Xtalism/pen-plotter-marlin/SLDPRT/CNC_FINAL.SLDASM

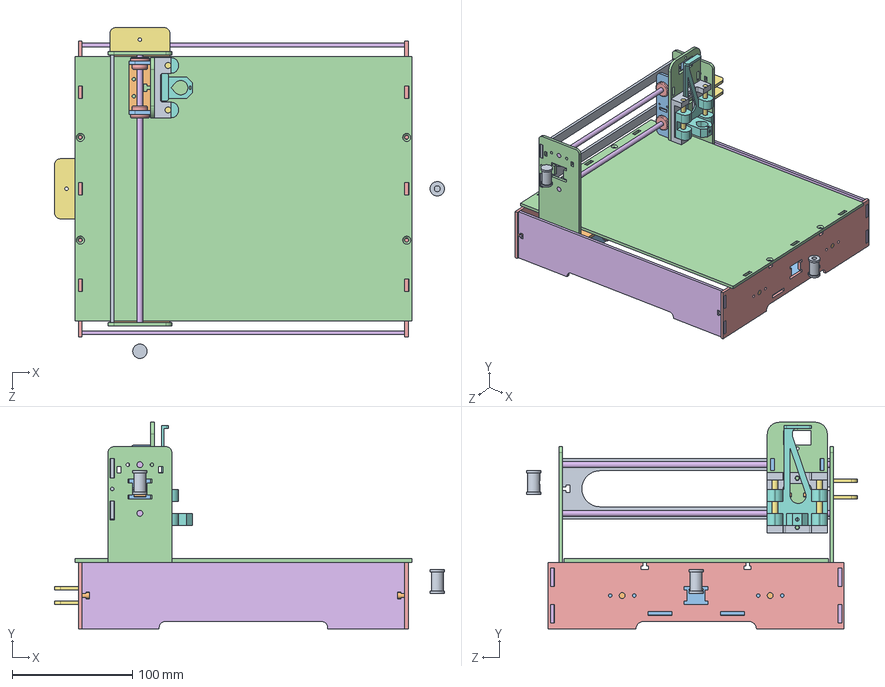
[picture p44: CAD file, 2025-09-09]
SLDPRT/CNC_FINAL.SLDASM
324.1 x 171.7 x 275.0 mm
SoporteY_CNC x 2
SoporteBuje_CNC x 2
BaseY
FronteY_CNC
SoportePequeno_CNC x 2
BASERODAMIENTO_CNC x 4
EjeCY_CNC x 2
Bujepr_CNC x 8
SoporteZ_CNC
SoporteTZ_CNC x 2
SoporteZP_CNC
BaseLapiz_CNC
EjeMovil_CNC
CilindroY_CNC x 2
Laterales_CNC x 2
Frontales_CNC x 2
Base_CNC
Soporte_CNC
CilindroX_CNC x 2
Buje_Motor_CNC x 2
