Xtalism/pen-plotter-marlin/SLDPRT/SoporteTZ_CNC.SLDPRT

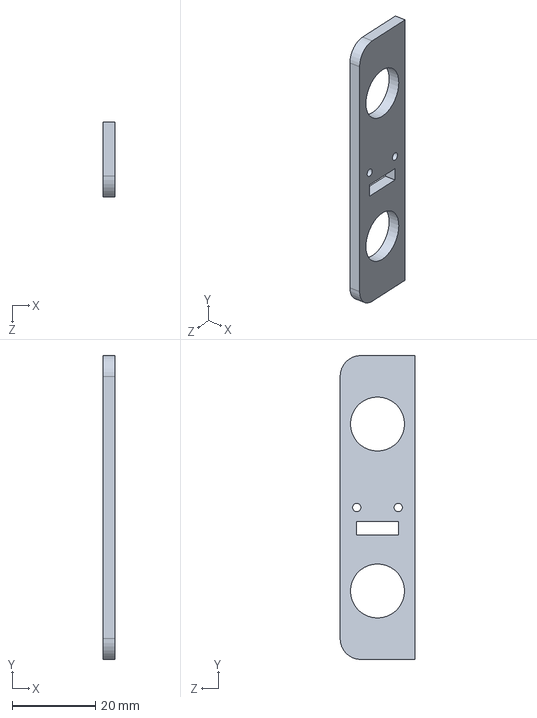
[picture p58: CAD file, 2025-09-09]
SLDPRT/SoporteTZ_CNC.SLDPRT
3.00 x 73.2 x 18.0 mm
