Xtalism/pen-plotter-marlin/SLDPRT/SoporteY_CNC.SLDPRT

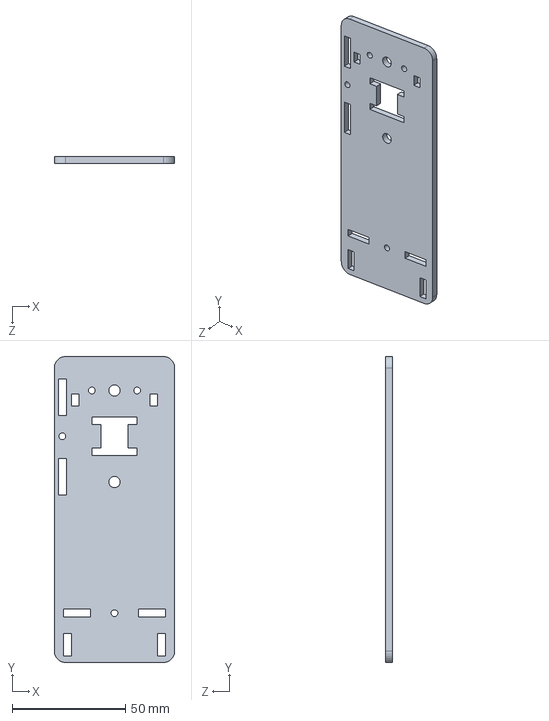
[picture p59: CAD file, 2025-09-09]
SLDPRT/SoporteY_CNC.SLDPRT
53.1 x 135.0 x 3.00 mm
