Xtalism/pen-plotter-marlin/SLDPRT/BaseLapiz_CNC.SLDPRT

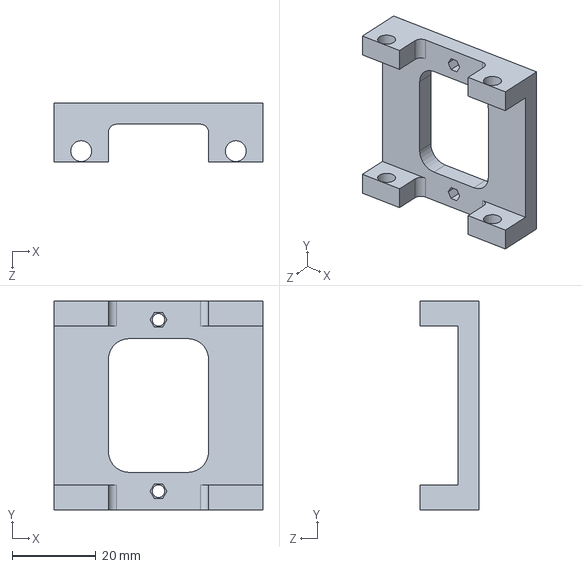
[picture p60: CAD file, 2025-09-09]
SLDPRT/BaseLapiz_CNC.SLDPRT
50.0 x 50.0 x 14.0 mm
