Xtalism/pen-plotter-marlin/SLDPRT/BaseY.SLDPRT

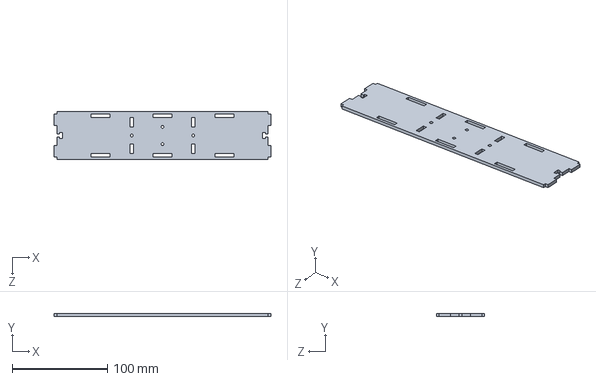
[picture p61: CAD file, 2025-09-09]
SLDPRT/BaseY.SLDPRT
228.0 x 3.00 x 50.0 mm
