Xtalism/pen-plotter-marlin/SLDPRT/SoporteZP_CNC.SLDPRT

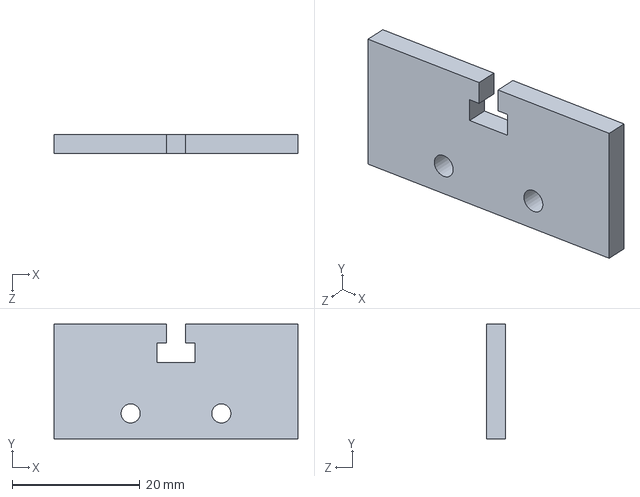
[picture p62: CAD file, 2025-09-09]
SLDPRT/SoporteZP_CNC.SLDPRT
38.2 x 18.0 x 3.00 mm
