Xtalism/pen-plotter-marlin/SLDPRT/CilindroX_CNC.SLDPRT

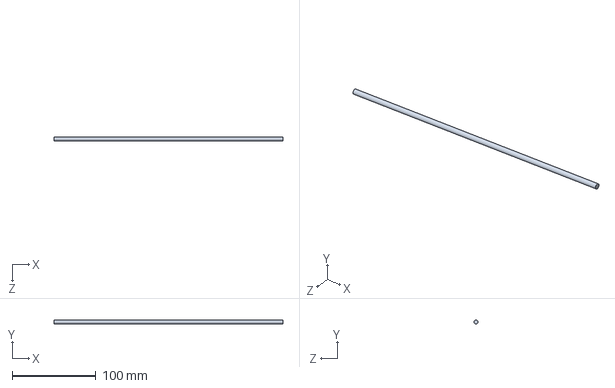
[picture p63: CAD file, 2025-09-09]
SLDPRT/CilindroX_CNC.SLDPRT
274.0 x 5.00 x 5.00 mm
