Xtalism/pen-plotter-marlin/SLDPRT/BASERODAMIENTO_CNC.SLDPRT

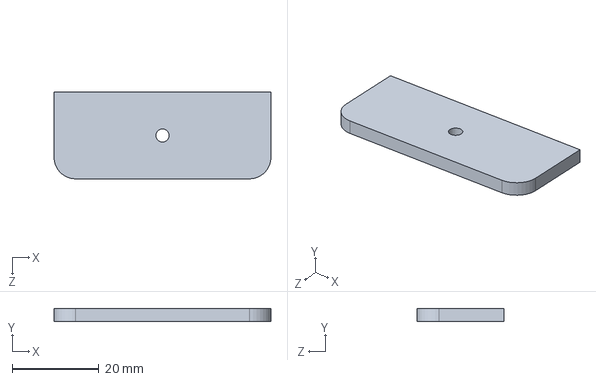
[picture p64: CAD file, 2025-09-09]
SLDPRT/BASERODAMIENTO_CNC.SLDPRT
50.0 x 3.00 x 20.0 mm
