Xtalism/pen-plotter-marlin/SLDPRT/SoporteMotor_CNC.SLDPRT

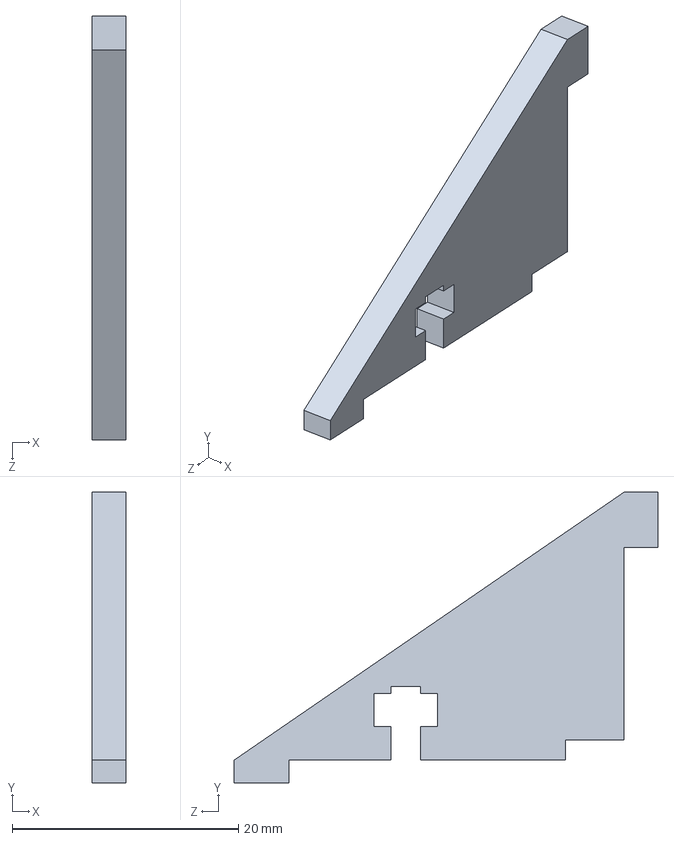
[picture p65: CAD file, 2025-09-09]
SLDPRT/SoporteMotor_CNC.SLDPRT
3.00 x 25.7 x 37.5 mm
