Xtalism/pen-plotter-marlin/SLDPRT/EjeMovil_CNC.SLDPRT

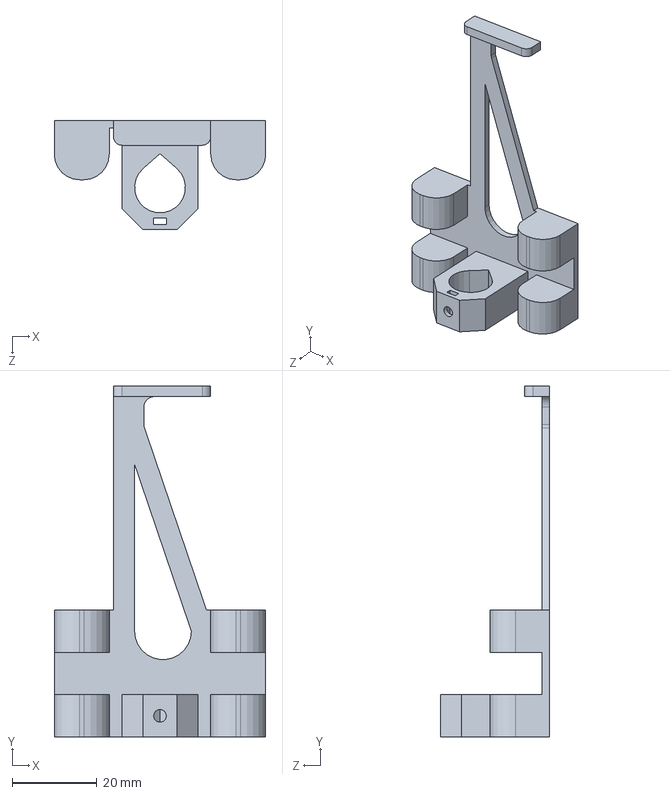
[picture p66: CAD file, 2025-09-09]
SLDPRT/EjeMovil_CNC.SLDPRT
50.0 x 83.0 x 25.9 mm
