Xtalism/pen-plotter-marlin/SLDPRT/EjeCY_CNC.SLDPRT

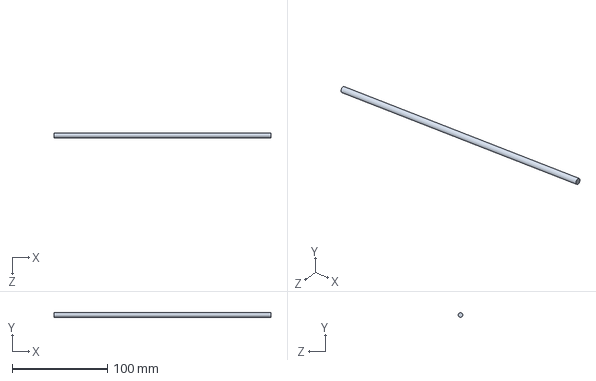
[picture p67: CAD file, 2025-09-09]
SLDPRT/EjeCY_CNC.SLDPRT
228.0 x 5.00 x 5.00 mm
