Xtalism/pen-plotter-marlin/SLDPRT/Blueprints/EJE Z.pdf

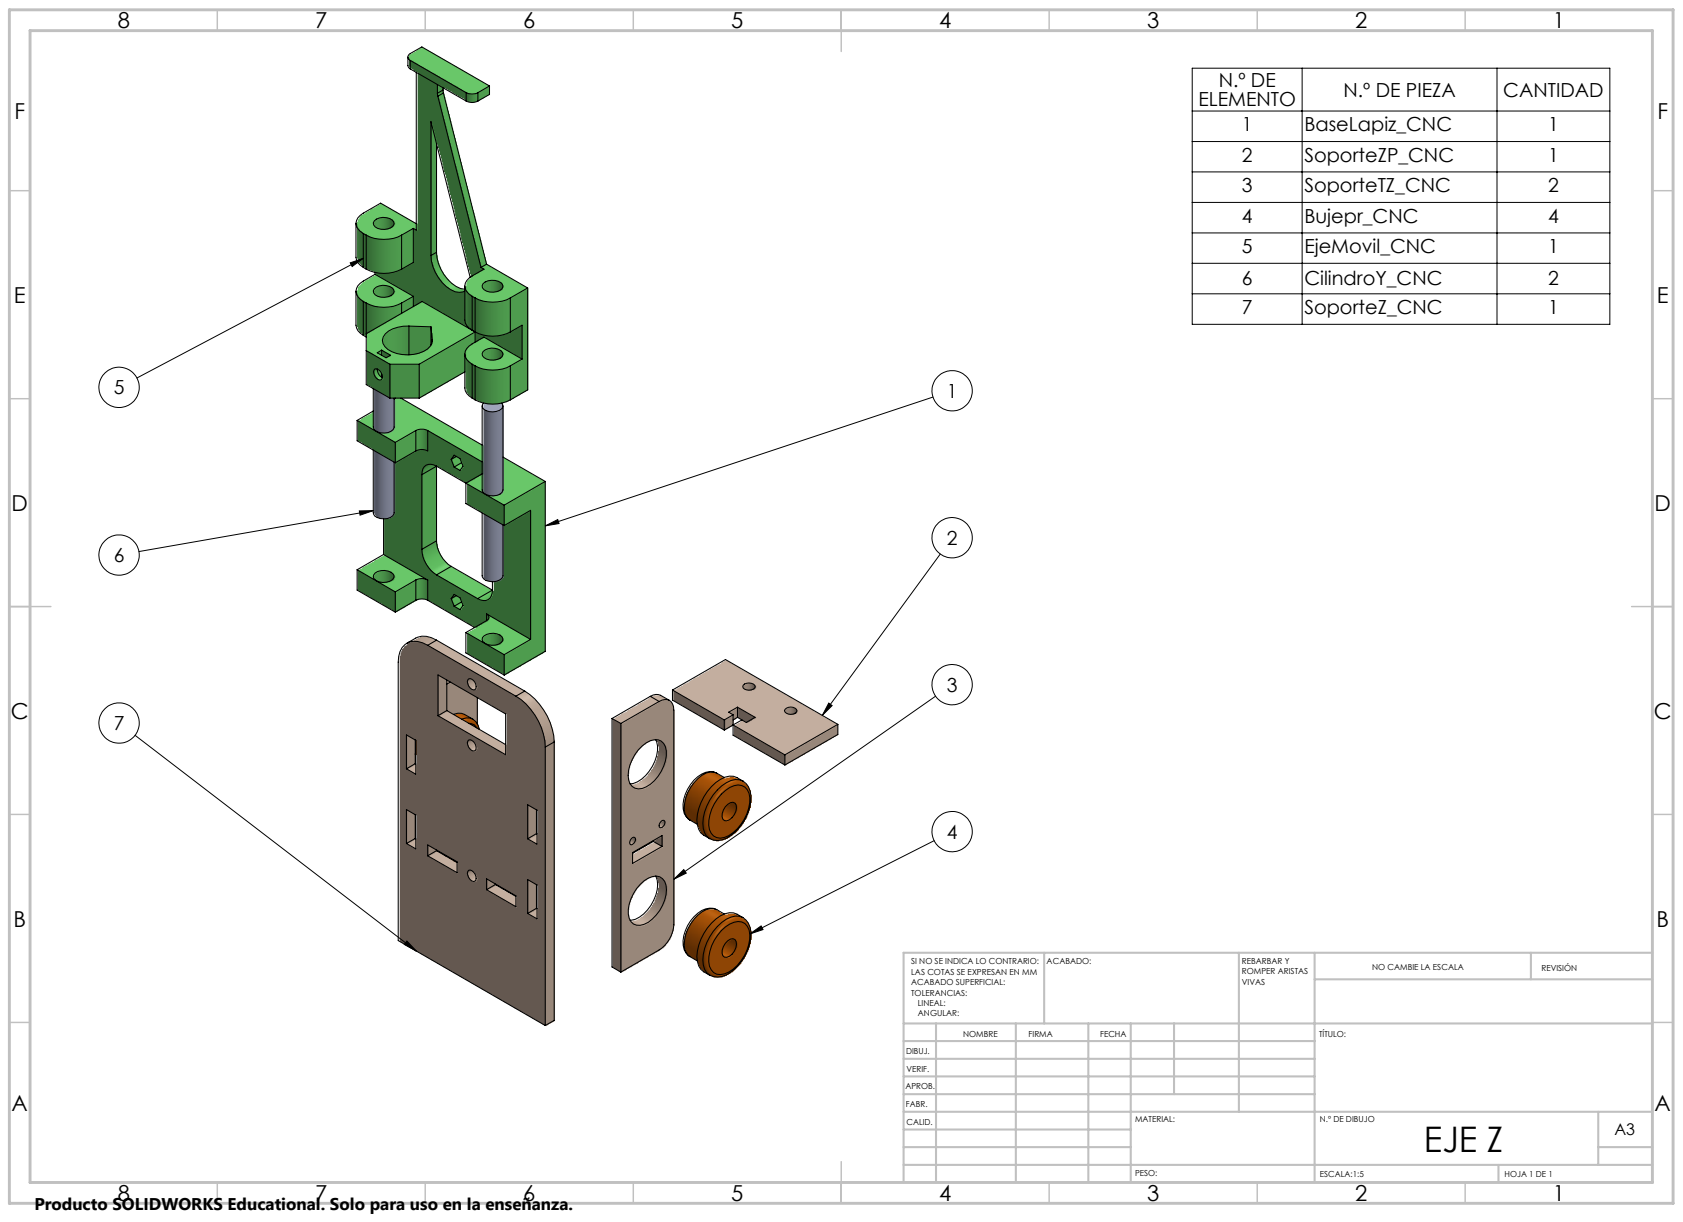
[picture p75: page 1]
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

N.º DE ELEMENTO | N.º DE PIEZA | CANTIDAD
1 | BaseLapiz_CNC | 1
2 | SoporteZP_CNC | 1
3 | SoporteTZ_CNC | 2
4 | Bujepr_CNC | 4
5 | EjeMovil_CNC | 1
6 | CilindroY_CNC | 2
7 | SoporteZ_CNC | 1

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

NOMBRE | FIRMA | FECHA | | | | TÍTULO:

DIBUJ.
VERIF.
APROB.
FABR.
CALID. | | | | MATERIAL: | N.º DE DIBUJO EJE Z | A3

Producto SOLIDWORKS Educational. Solo para uso en la enseñanza.
